jaksg82/FanControl_IOT/PLC/Debug.h

#ifndef DEBUG_H
#define DEBUG_H

#include <stdint.h>

class Debug {
public:
	template <class T>
	static void print(T value) {
		if (Serial) {
			Serial.print(value);
		}
	}

	template <class T>
	static void println(T value) {
		if (Serial) {
			Serial.println(value);
		}
	}

  static void println() {
    if (Serial) {
      Serial.println();
    }
  }

};

#endif
